FPGA-Computer/KVM-Switch/Hardware/Acive Or'ing (optional)/LT Spice simulation/Active or'ing diode discrete -0.asc

M1: pmos; ""
M2: pmos; ""
Q1: pnp2; 2N4126
Q2: pnp2; 2N3906
Q3: pnp2; 2N3906
Q4: pnp2; 2N2905A
R1: res; 100K
R2: res; 47K
R3: res; 5r
R4: res; 100K
R5: res; 47K
V1: voltage; 5V; Rser=1R
V2: voltage; PULSE(0V 5.0V 10ms 100ms 10ms 10ms 120ms 100); Rser=1R
Named nets: 0
.include "Si2307bd.lib"
.tran 150ms
