FPGA-Computer/KVM-Switch/KVM-Hotkey/stm8_interrupt_vector.h

/*
 * stm8_interrupt_vector.h
 *
 * Created: February-10-17, 9:47:05 PM
 *  Author: K. C. Lee
 * Copyright (c) 2017 by K. C. Lee
 
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
 If not, see http://www.gnu.org/licenses/gpl-3.0.en.html 
 */ 

#ifndef TRAP
#define TRAP Default_IRQ_Handler
#endif

#ifndef IRQ0
#define IRQ0 Default_IRQ_Handler
#endif

#ifndef IRQ1
#define IRQ1 Default_IRQ_Handler
#endif

#ifndef IRQ2
#define IRQ2 Default_IRQ_Handler
#endif

#ifndef IRQ3
#define IRQ3 Default_IRQ_Handler
#endif

#ifndef IRQ4
#define IRQ4 Default_IRQ_Handler
#endif

#ifndef IRQ5
#define IRQ5 Default_IRQ_Handler
#endif

#ifndef IRQ6
#define IRQ6 Default_IRQ_Handler
#endif

#ifndef IRQ7
#define IRQ7 Default_IRQ_Handler
#endif

#ifndef IRQ8
#define IRQ8 Default_IRQ_Handler
#endif

#ifndef IRQ9
#define IRQ9 Default_IRQ_Handler
#endif

#ifndef IRQ10
#define IRQ10 Default_IRQ_Handler
#endif

#ifndef IRQ11
#define IRQ11 Default_IRQ_Handler
#endif

#ifndef IRQ12
#define IRQ12 Default_IRQ_Handler
#endif

#ifndef IRQ13
#define IRQ13 Default_IRQ_Handler
#endif

#ifndef IRQ14
#define IRQ14 Default_IRQ_Handler
#endif

#ifndef IRQ15
#define IRQ15 Default_IRQ_Handler
#endif

#ifndef IRQ16
#define IRQ16 Default_IRQ_Handler
#endif

#ifndef IRQ17
#define IRQ17 Default_IRQ_Handler
#endif

#ifndef IRQ18
#define IRQ18 Default_IRQ_Handler
#endif

#ifndef IRQ19
#define IRQ19 Default_IRQ_Handler
#endif

#ifndef IRQ20
#define IRQ20 Default_IRQ_Handler
#endif

#ifndef IRQ21
#define IRQ21 Default_IRQ_Handler
#endif

#ifndef IRQ22
#define IRQ22 Default_IRQ_Handler
#endif

#ifndef IRQ23
#define IRQ23 Default_IRQ_Handler
#endif

#ifndef IRQ24
#define IRQ24 Default_IRQ_Handler
#endif

#ifndef IRQ25
#define IRQ25 Default_IRQ_Handler
#endif

#ifndef IRQ26
#define IRQ26 Default_IRQ_Handler
#endif

#ifndef IRQ27
#define IRQ27 Default_IRQ_Handler
#endif

#ifndef IRQ28
#define IRQ28 Default_IRQ_Handler
#endif

#ifndef IRQ29
#define IRQ29 Default_IRQ_Handler
#endif
